X-AT/x-at-arduino/fw/wall_time.h

/**
 * @brief Wall time timer funrcions.
 *
 * Ported from arduino wiring.c.
 */

#ifndef _WALL_TIME_H_
#define _WALL_TIME_H_

void WallTime_Init(void);
unsigned long millis(void);
unsigned long micros(void);

#endif /* _WALL_TIME_H_ */
